Mona-zza/SlayPad/Images/image2.png

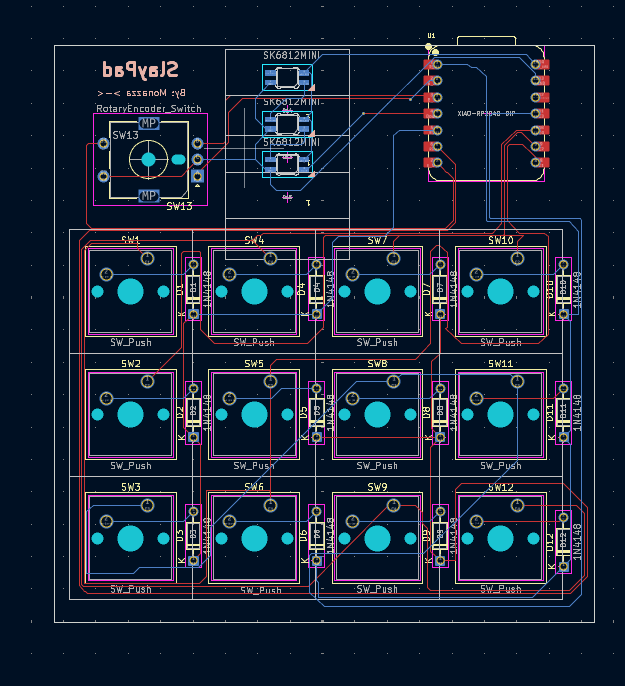
Images/image2.png
