Mona-zza/SlayPad/Images/image3.png

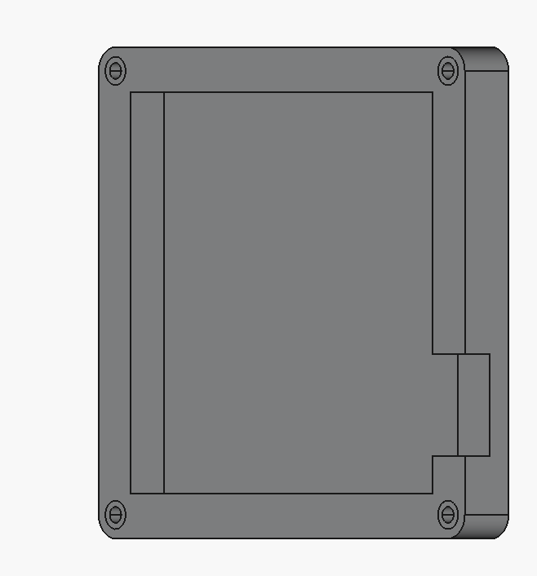
Images/image3.png
