Mona-zza/SlayPad/Images/image4.png

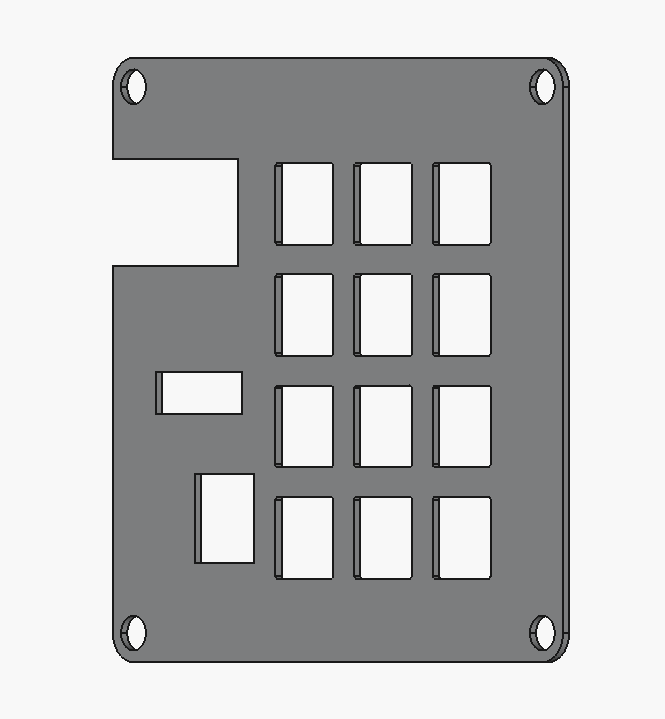
Images/image4.png
