Mona-zza/SlayPad/Images/image5.png

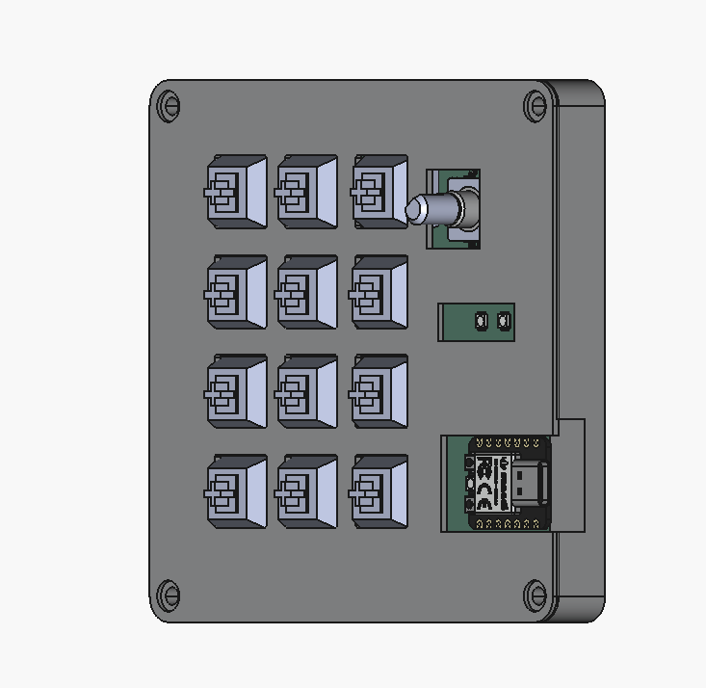
Images/image5.png
