Mona-zza/SlayPad/Images/image6.png

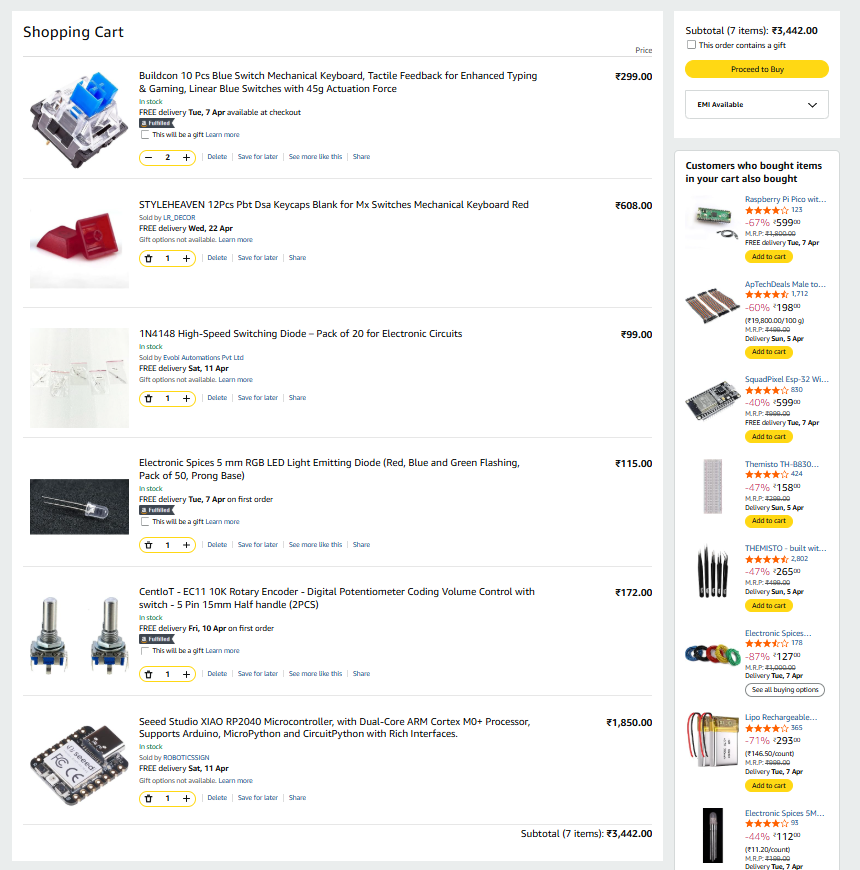
Images/image6.png
