Mona-zza/SlayPad/Images/image7.png

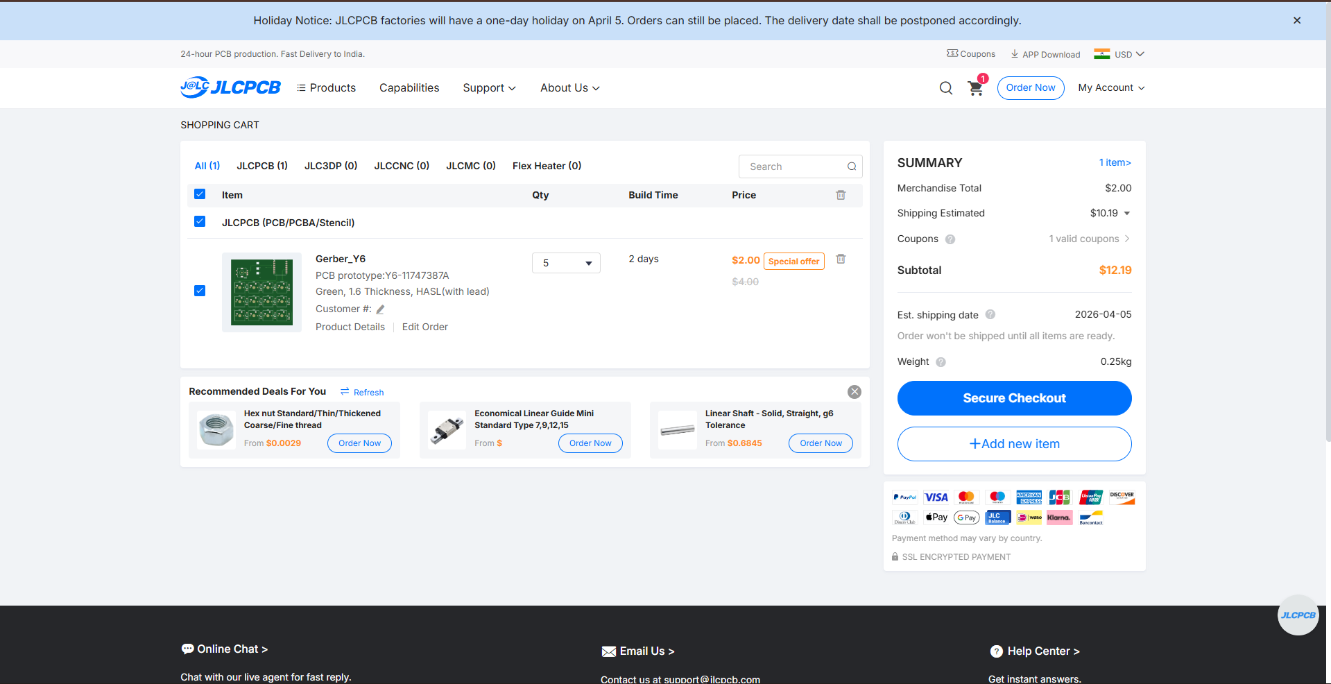
Images/image7.png
