Mona-zza/SlayPad/Images/image8.png

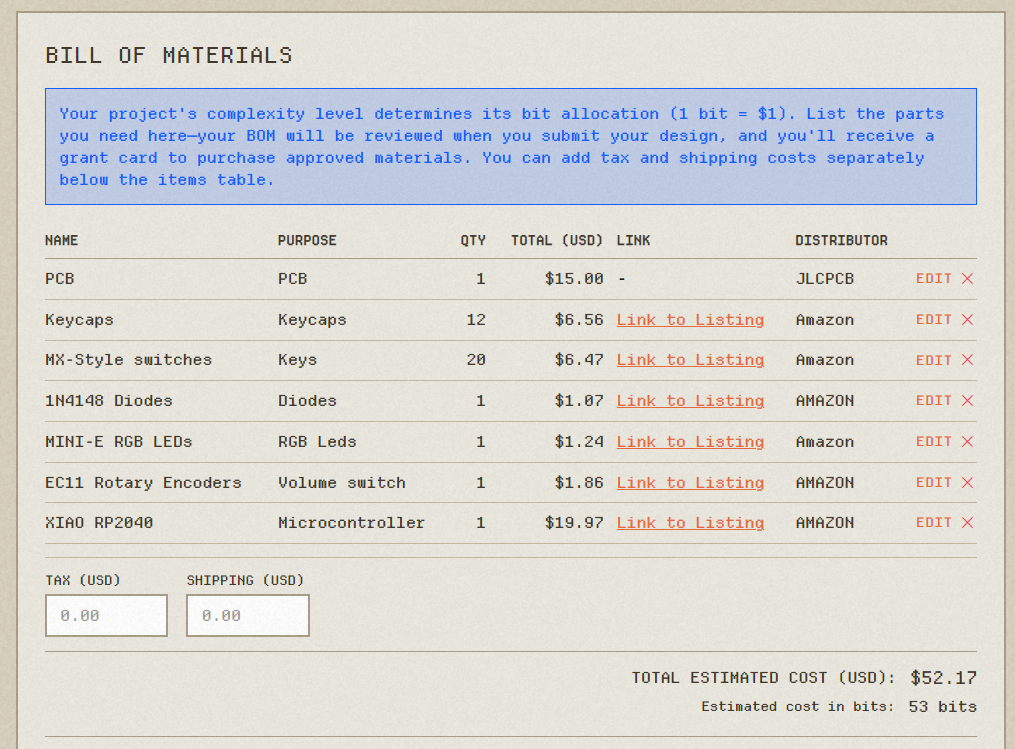
Images/image8.png
